TDiblik/7941W-rfid-card-cloner/simple/src/constants.h

#pragma once

#define DEBUG true
#define READ_125KHz_BUTTON 2
#define WRITE_125KHz_BUTTON 3
#define READ_13_56MHz_BUTTON 4
#define WRITE_13_56MHz_BUTTON 5
